jp112sdl/HB-RC-4-Dis-TH/Images/IMG_1487.jpg

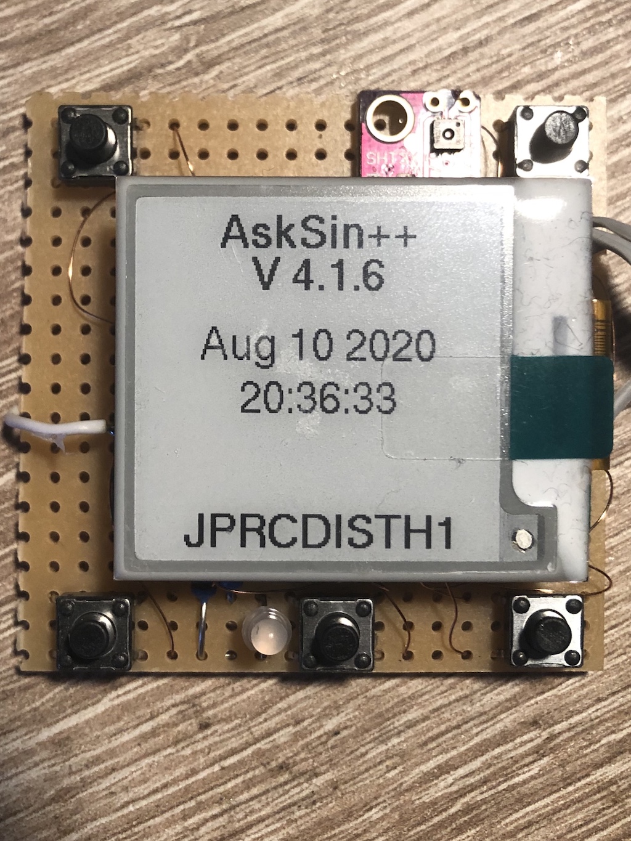
Images/IMG_1487.jpg
