jp112sdl/HB-RC-4-Dis-TH/Images/IMG_1631.jpg

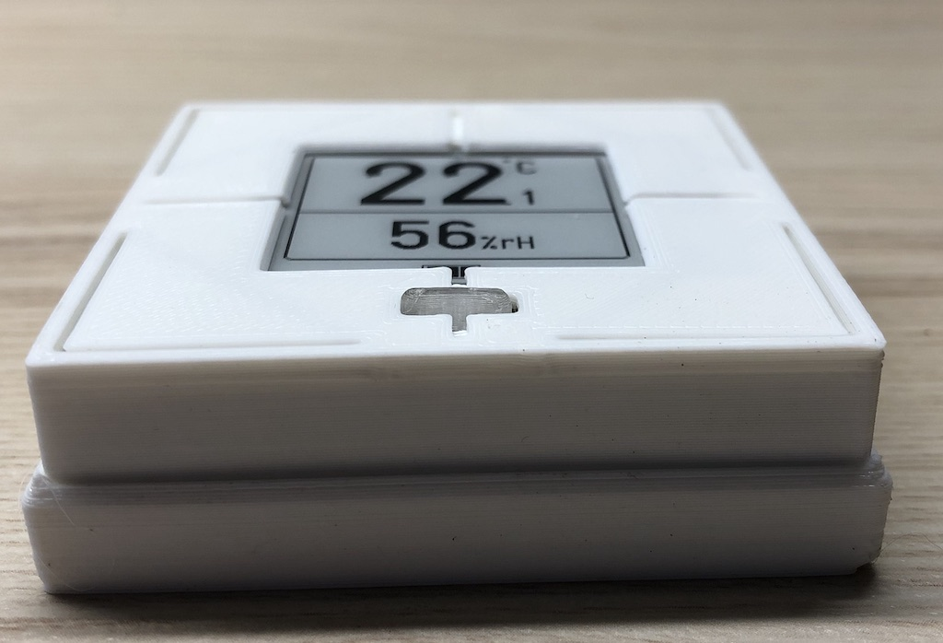
Images/IMG_1631.jpg
