jp112sdl/HB-RC-4-Dis-TH/Images/IMG_1633.jpg

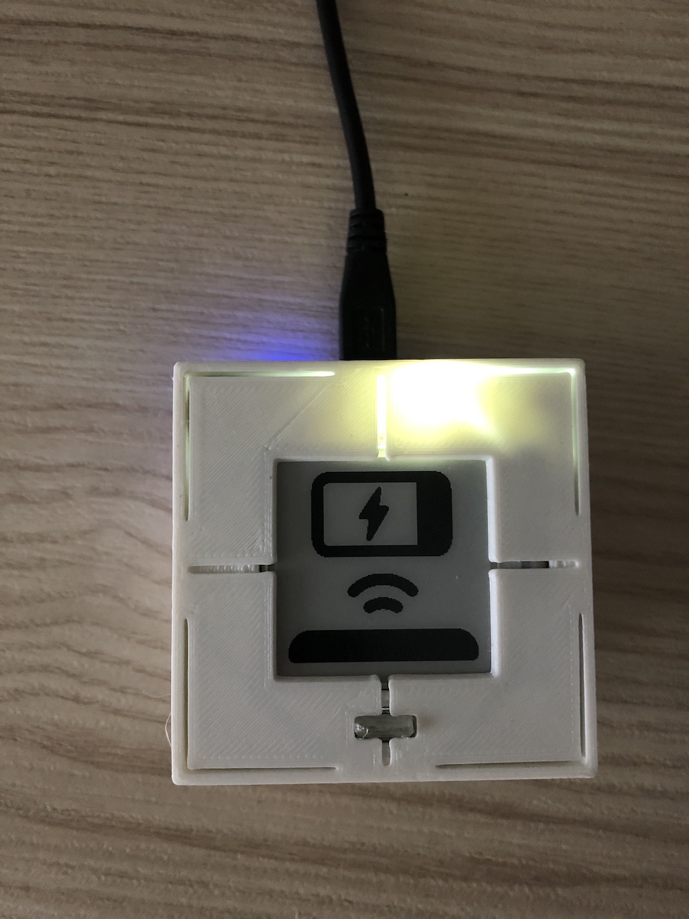
Images/IMG_1633.jpg
