jp112sdl/HB-RC-4-Dis-TH/Images/PCB1.jpg

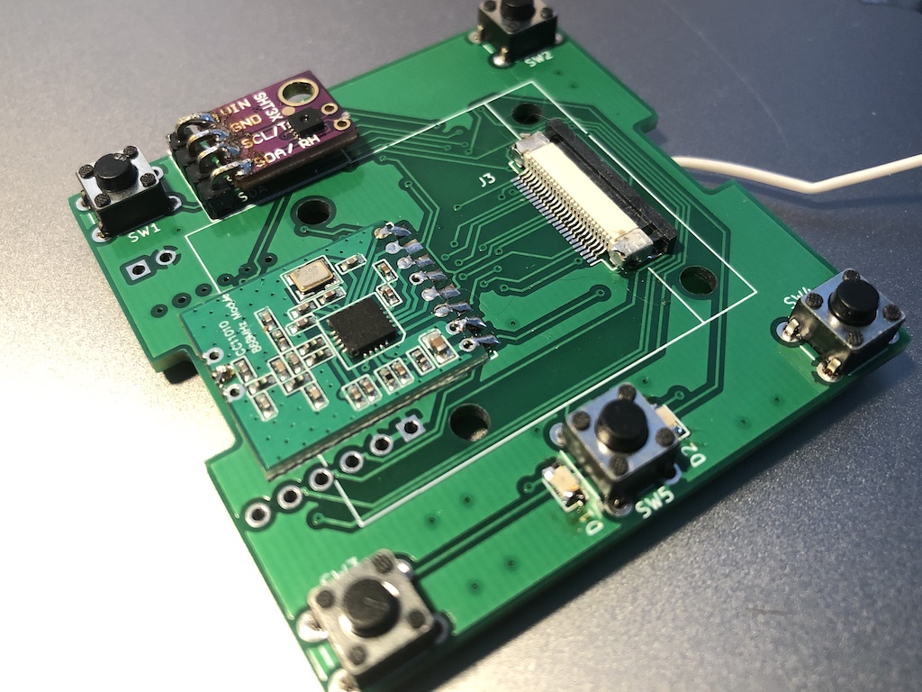
Images/PCB1.jpg
